karaaab/Sit-and-Move/Current-project-files/Models/SitNMove_schematic.kicad_sch

## KiCad design Current-project-files/Models/SitNMove_schematic.kicad_sch (2026-10-04)

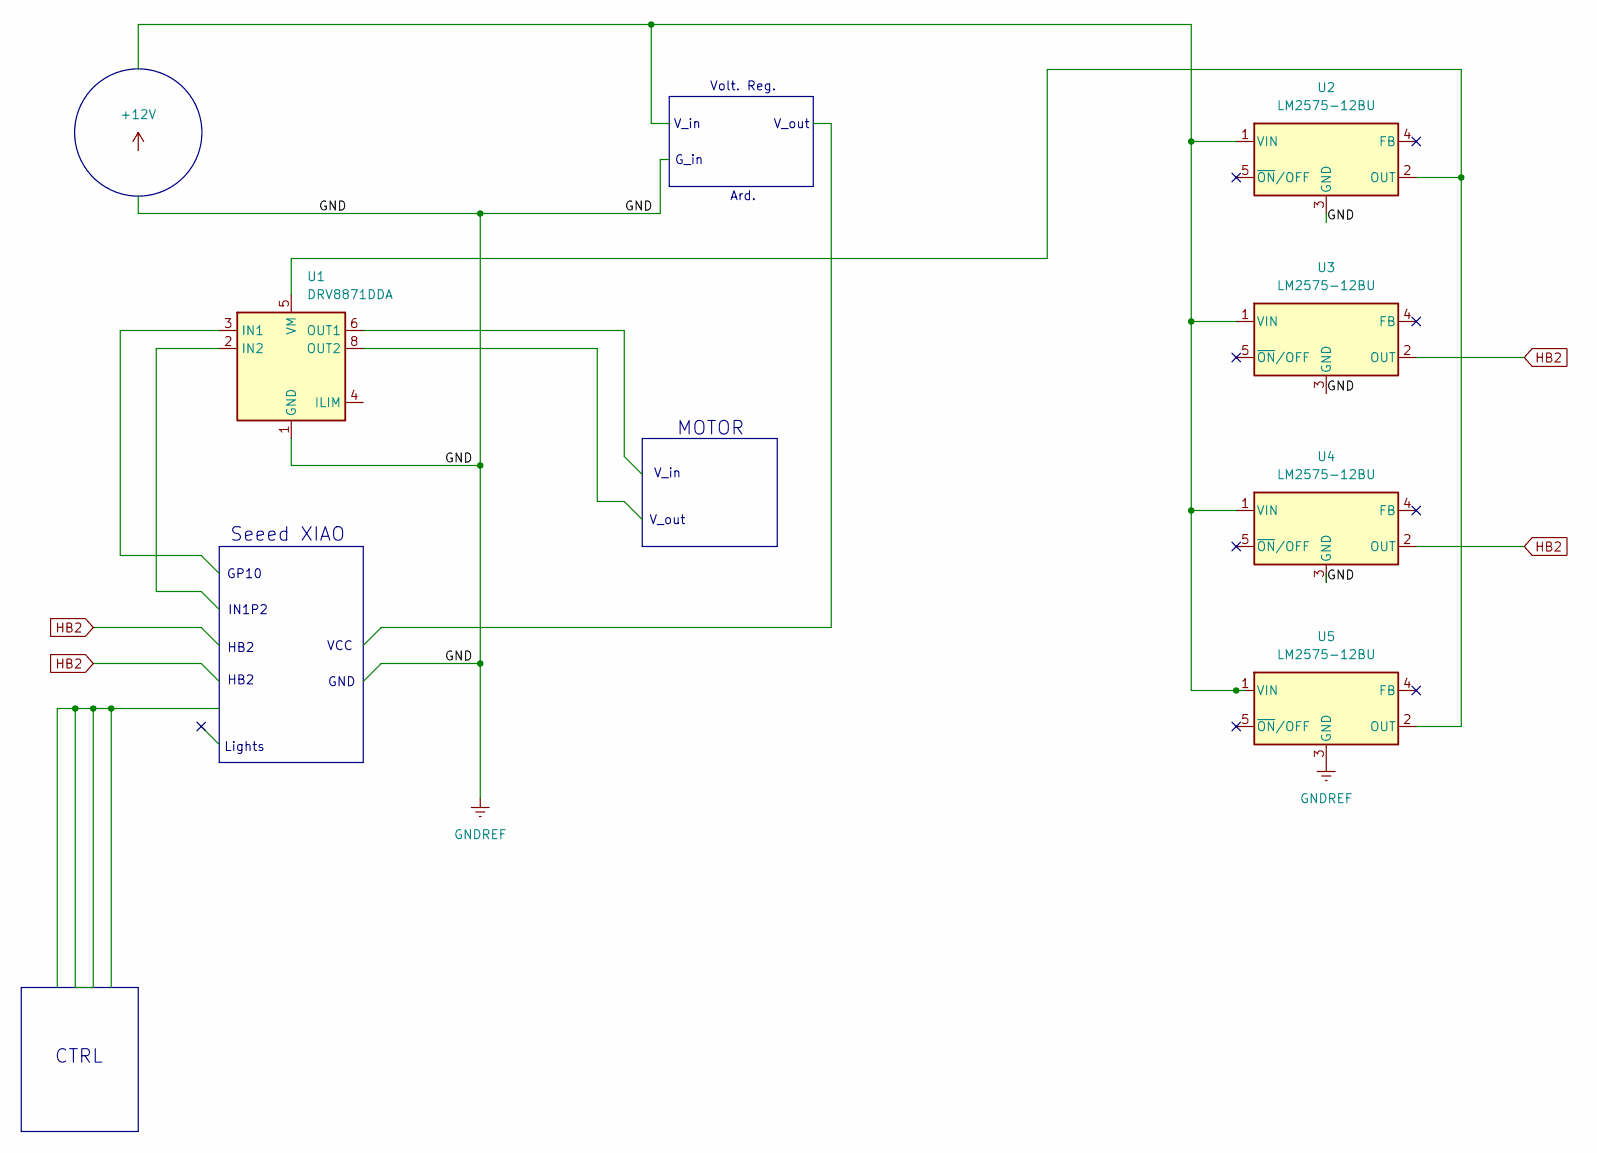
[picture p3: schematic SitNMove_schematic.kicad_sch]

Parts:
U1: DRV8871DDA; Texas_HTSOP-8-1EP_3.9x4.9mm_P1.27mm_EP2.95x4.9mm_Mask2.4x3.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
U2, U3, U4, U5: LM2575-12BU; TO-263-5_TabPin3

Connections:
GNDREF: U1.1 (GND), U1.7 (GND), U1.9 (GND), U2.3 (GND), U3.3 (GND), U4.3 (GND), U5.3 (GND)
HB2: U3.2 (OUT), U4.2 (OUT)
unnamed: U1.5 (VM), U2.2 (OUT), U5.2 (OUT)
unnamed: U2.1 (VIN), U3.1 (VIN), U4.1 (VIN), U5.1 (VIN)

Notes on the sheet:
V_out
Seeed XIAO
GND
MOTOR
Volt. Reg.
HB2
IN1P2
V_in
Ard.
Lights
CTRL
VCC
GP10
G_in
V_in
